sinara-hw/Phaser/Calc_SIM/LT1763_DC368.asc

C1: cap; 2µ; Rser=1m
C2: cap; 10n
C3: cap; 1µ
C4: cap; 20µ; Rser=0.7
I1: current; PULSE(0 0.1 0.01 100n 100n 10m 10m 10000)
R1: res; 43k
R2: res; 9.1k
Rload: res; 10
U1: LT1763
V1: voltage; PWL(0 0 1 7.4)
Named nets: 0, OUT, IN
.tran 0 4.9902 4.99 startup
Note:
  If the simulation model is not found please update with the "Sync Release" command from the "Tools" menu.
  It remains the customer's responsibility to verify proper and reliable operation in the actual application.
  Component substitution and printed circuit board layout may significantly affect circuit performance or reliability.
  Contact your local sales representative for assistance. This circuit is distributed to customers only for use with LTC parts.
  Copyright © 2011 Linear Technology Inc. All rights reserved.
LT1763 - 500mA, Low Noise, LDO µPower Regulators
Input: 10V     Output: 2.5V @ 500mA
